Aces-Electronics/ae-landy-heater-controller/product_images/Screenshot 2024-09-10 at 9.40.45 PM.png

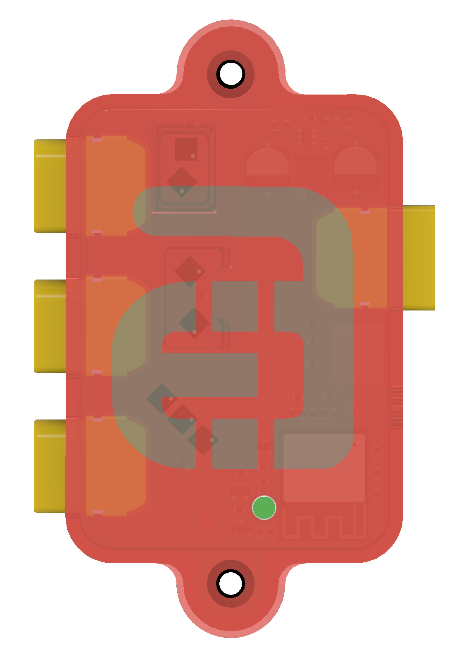
product_images/Screenshot 2024-09-10 at 9.40.45 PM.png
